marmaladelane/slip/IMG_8432.jpg

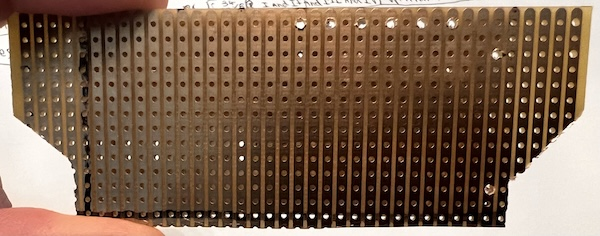
IMG_8432.jpg
